WizardEclipse/MORPHEUS/flash_to_testi/src/main.cpp

#include <Arduino.h>
#include <Wire.h>
#include <Adafruit_SSD1306.h>

#define SCREEN_WIDTH 128
#define SCREEN_HEIGHT 64
#define OLED_RESET -1
Adafruit_SSD1306 display_handler(SCREEN_WIDTH, SCREEN_HEIGHT, &Wire, OLED_RESET);

void setup() {
	display_handler.begin(SSD1306_SWITCHCAPVCC, 0x3C);
	display_handler.clearDisplay();
	display_handler.setTextSize(1);
	display_handler.setTextColor(SSD1306_WHITE);
	display_handler.setCursor(0,0);
	display_handler.println("TESTING FLASH TIME IS: ");
	display_handler.println(__TIME__);
	display_handler.display();
}

void loop(){}
